johan-adriaans/SyringeHelper/stl-examples/BDUltraFine-U100-0-to-1.stl

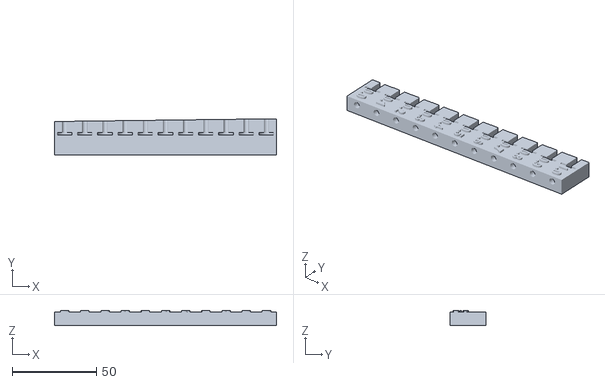
[picture p19: CAD file, 2025-03-12]
stl-examples/BDUltraFine-U100-0-to-1.stl
132.0 x 21.5 x 9.00
