johan-adriaans/SyringeHelper/stl-examples/BDUltraFine-U100-3-to-4.stl

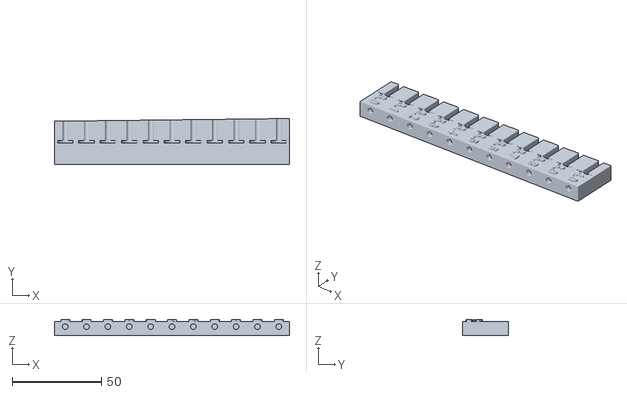
[picture p20: CAD file, 2025-03-12]
stl-examples/BDUltraFine-U100-3-to-4.stl
132.0 x 25.6 x 9.00
