johan-adriaans/SyringeHelper/stl-examples/SolVet-U40-1.6-to-2.5.stl

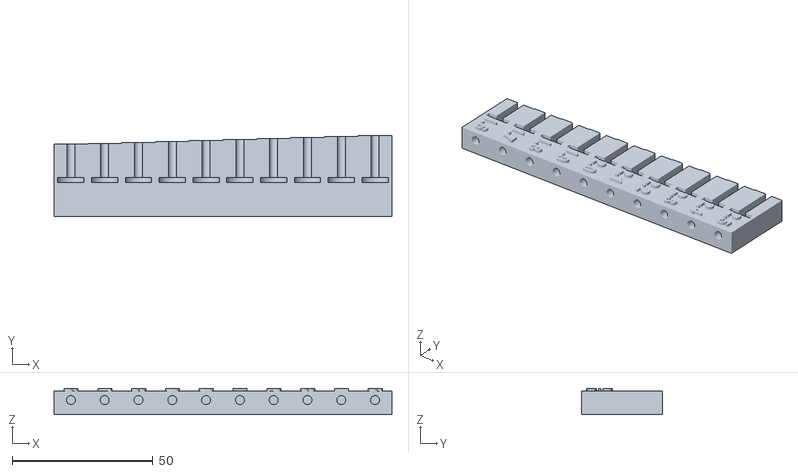
[picture p21: CAD file, 2024-09-01]
stl-examples/SolVet-U40-1.6-to-2.5.stl
120.0 x 28.8 x 9.40
