johan-adriaans/SyringeHelper/stl-examples/SolVet-U40-0.05-to-0.5.stl

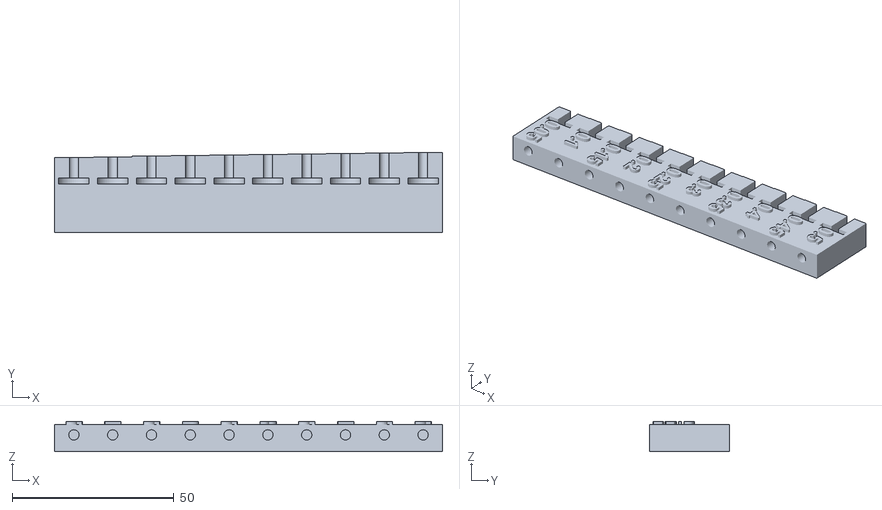
[picture p22: CAD file, 2024-09-01]
stl-examples/SolVet-U40-0.05-to-0.5.stl
120.0 x 24.9 x 9.40
