johan-adriaans/SyringeHelper/stl-examples/SolVet-U40-3.75-to-6.5.stl

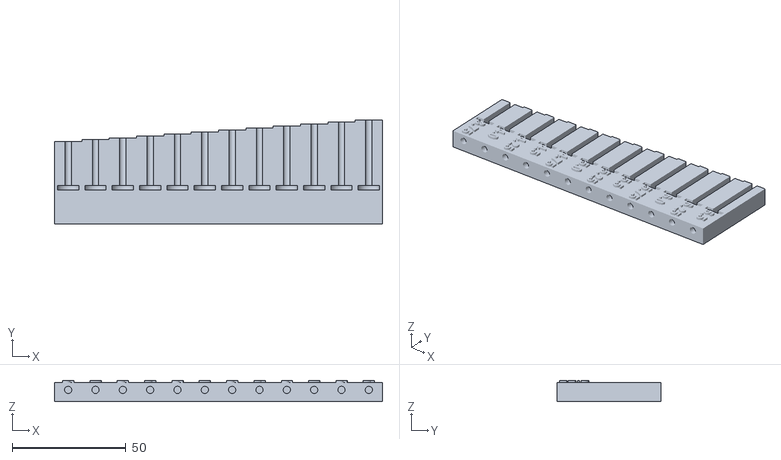
[picture p23: CAD file, 2024-09-01]
stl-examples/SolVet-U40-3.75-to-6.5.stl
144.0 x 45.6 x 9.40
