johan-adriaans/SyringeHelper/stl-examples/SolVet-U40-calibration.stl

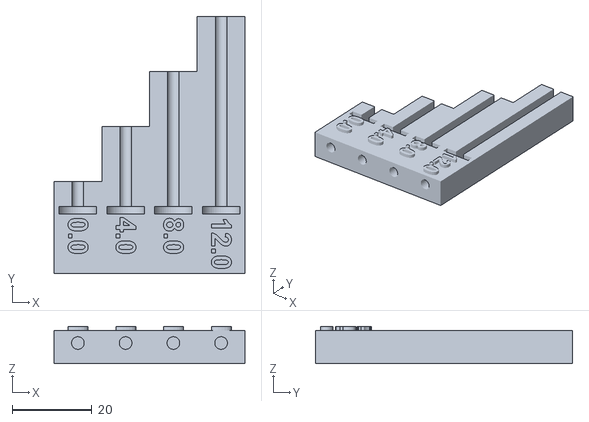
[picture p24: CAD file, 2024-09-01]
stl-examples/SolVet-U40-calibration.stl
48.0 x 64.6 x 9.40
