johan-adriaans/SyringeHelper/stl-examples/SolVet-U40-0.75-to-3.5.stl

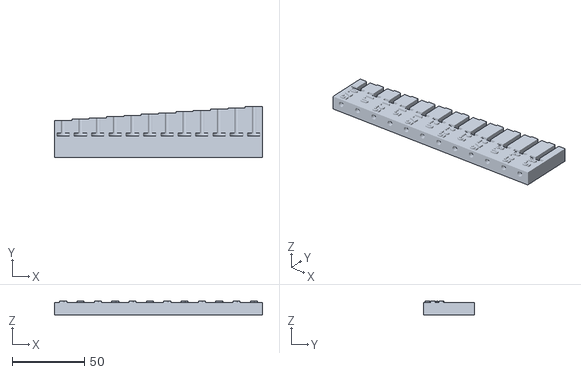
[picture p25: CAD file, 2024-09-01]
stl-examples/SolVet-U40-0.75-to-3.5.stl
144.0 x 35.2 x 9.40
