johan-adriaans/SyringeHelper/stl-examples/SolVet-U100-1-to-3.5.stl

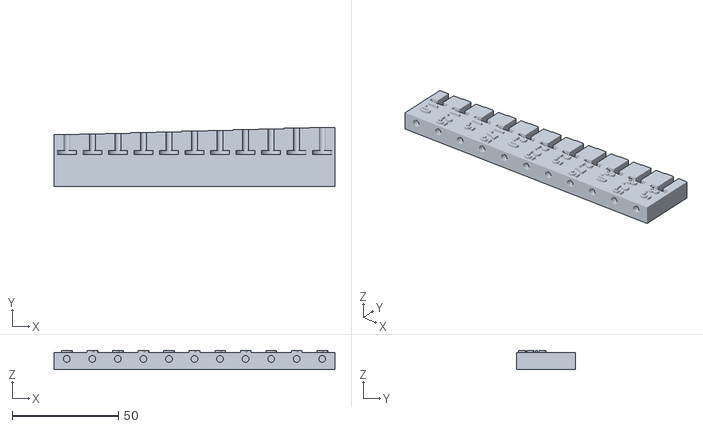
[picture p26: CAD file, 2024-05-23]
stl-examples/SolVet-U100-1-to-3.5.stl
132.0 x 27.9 x 9.00
