johan-adriaans/SyringeHelper/stl-examples/SolVet-U100-3.75-to-6.stl

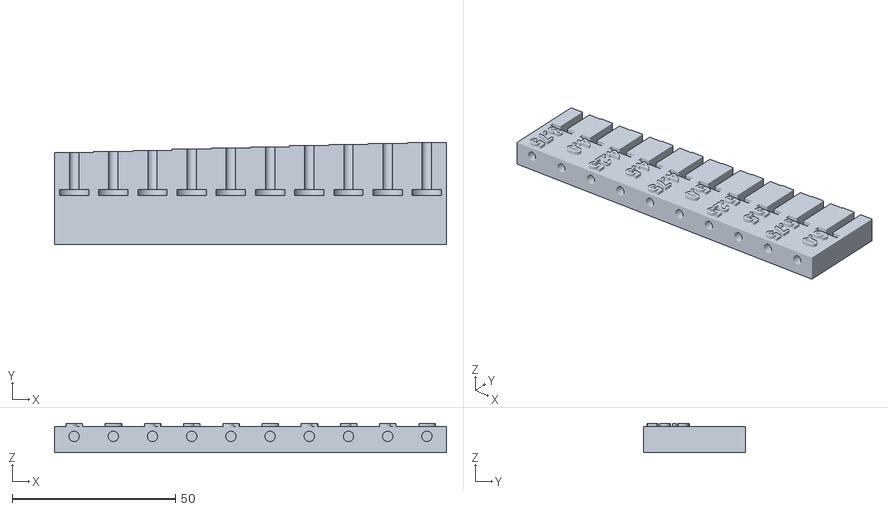
[picture p27: CAD file, 2024-05-23]
stl-examples/SolVet-U100-3.75-to-6.stl
120.0 x 31.3 x 9.00
