johan-adriaans/SyringeHelper/stl-examples/SolVet-U100-6-to-7.stl

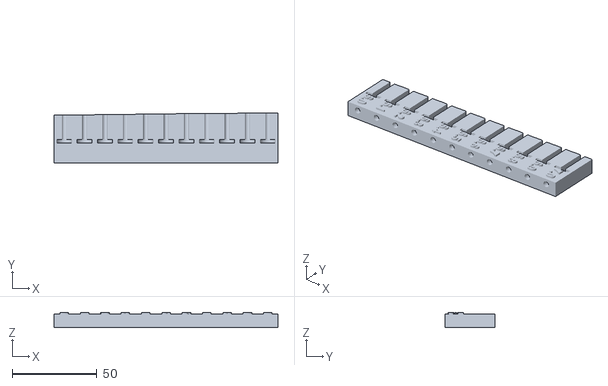
[picture p28: CAD file, 2024-05-23]
stl-examples/SolVet-U100-6-to-7.stl
132.0 x 29.7 x 9.00
