johan-adriaans/SyringeHelper/stl-examples/SolVet-U100-4-to-5.stl

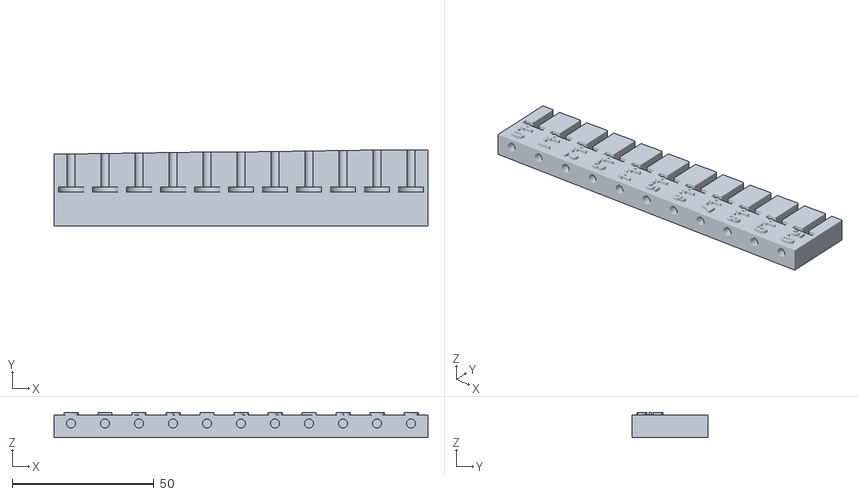
[picture p29: CAD file, 2024-05-23]
stl-examples/SolVet-U100-4-to-5.stl
132.0 x 26.9 x 9.00
