johan-adriaans/SyringeHelper/stl-examples/SolVet-U100-7-to-8.stl

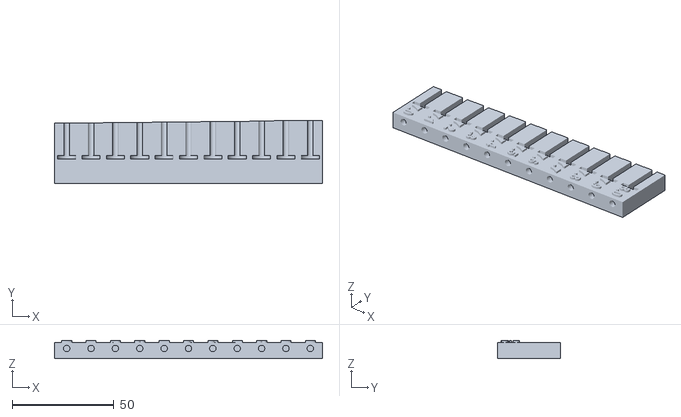
[picture p30: CAD file, 2024-05-23]
stl-examples/SolVet-U100-7-to-8.stl
132.0 x 31.1 x 9.00
