johan-adriaans/SyringeHelper/stl-examples/SolVet-U100-8-to-9.stl

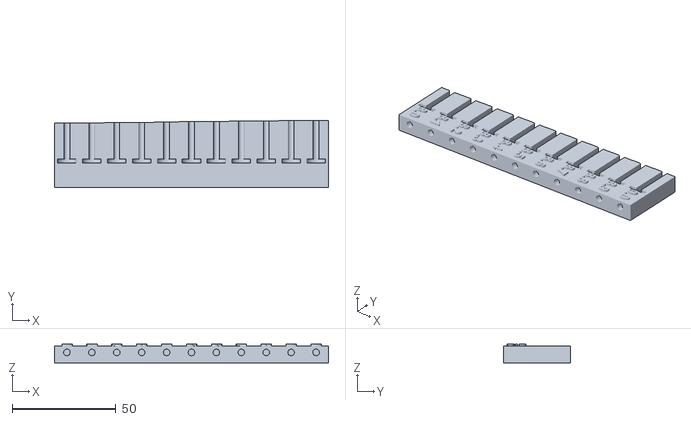
[picture p31: CAD file, 2024-05-23]
stl-examples/SolVet-U100-8-to-9.stl
132.0 x 32.5 x 9.00
