johan-adriaans/SyringeHelper/stl-examples/SolVet-U100-calibration.stl

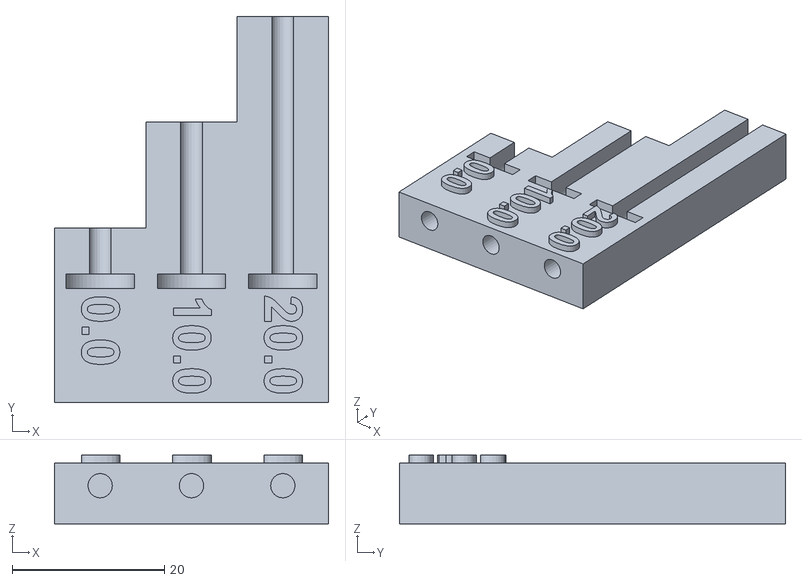
[picture p32: CAD file, 2024-05-23]
stl-examples/SolVet-U100-calibration.stl
36.0 x 50.8 x 9.00
