johan-adriaans/SyringeHelper/stl-examples/BDMicroFine-U100-4-to-5.stl

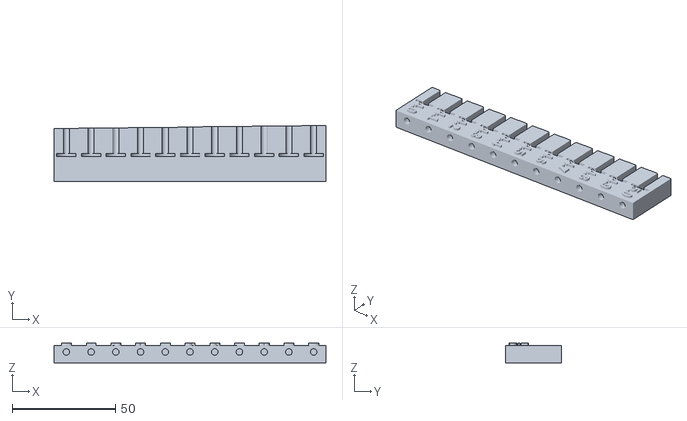
[picture p33: CAD file, 2023-01-15]
stl-examples/BDMicroFine-U100-4-to-5.stl
132.0 x 27.1 x 9.50
