johan-adriaans/SyringeHelper/stl-examples/BDMicroFine-U100-7-to-8.stl

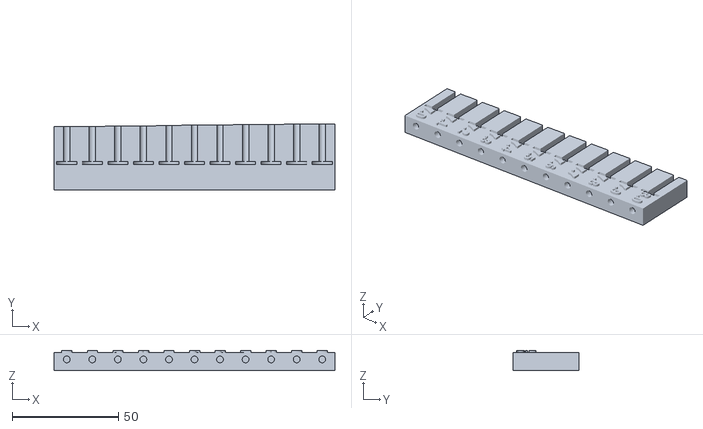
[picture p34: CAD file, 2023-01-15]
stl-examples/BDMicroFine-U100-7-to-8.stl
132.0 x 31.2 x 9.50
