johan-adriaans/SyringeHelper/stl-examples/BDMicroFine-U40-6-to-7.stl

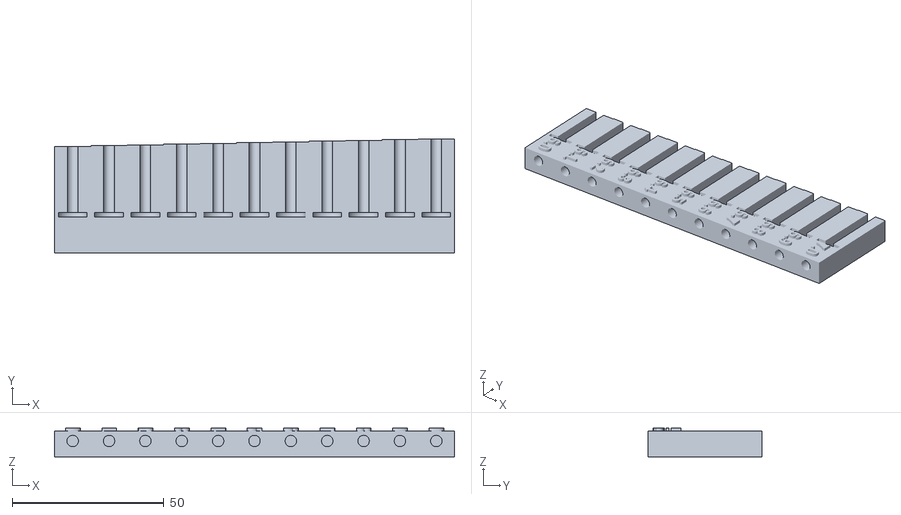
[picture p35: CAD file, 2023-01-15]
stl-examples/BDMicroFine-U40-6-to-7.stl
132.0 x 37.8 x 9.50
