johan-adriaans/SyringeHelper/stl-examples/BDMicroFine-U100-1-to-2.stl

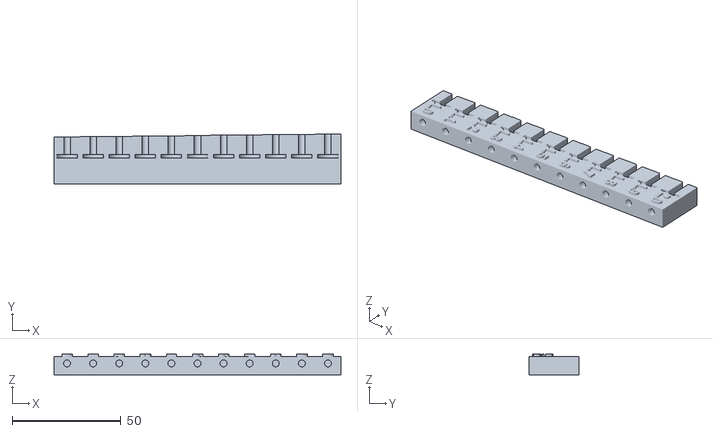
[picture p36: CAD file, 2023-01-15]
stl-examples/BDMicroFine-U100-1-to-2.stl
132.0 x 23.0 x 9.50
