johan-adriaans/SyringeHelper/stl-examples/BDMicroFine-U40-3-to-4.stl

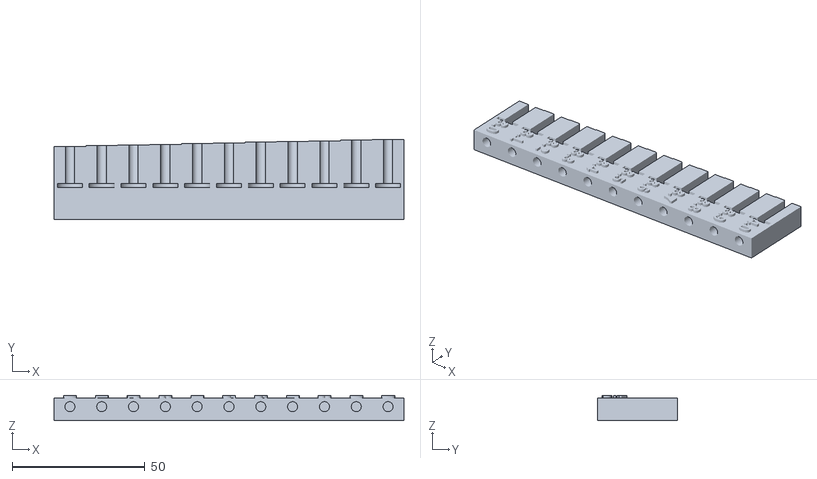
[picture p37: CAD file, 2023-01-15]
stl-examples/BDMicroFine-U40-3-to-4.stl
132.0 x 30.1 x 9.50
