johan-adriaans/SyringeHelper/stl-examples/BDMicroFine-U40-1-to-2.stl

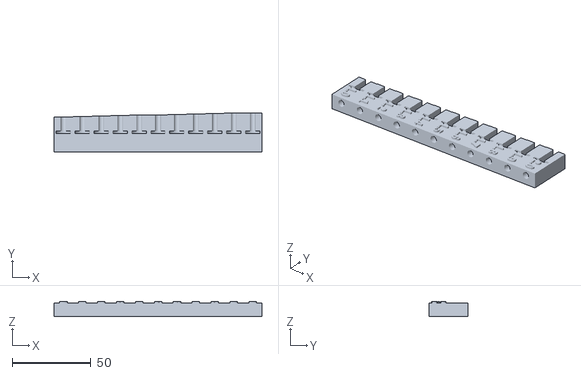
[picture p38: CAD file, 2023-01-15]
stl-examples/BDMicroFine-U40-1-to-2.stl
132.0 x 25.0 x 9.50
