johan-adriaans/SyringeHelper/stl-examples/BDMicroFine-U40-calibration.stl

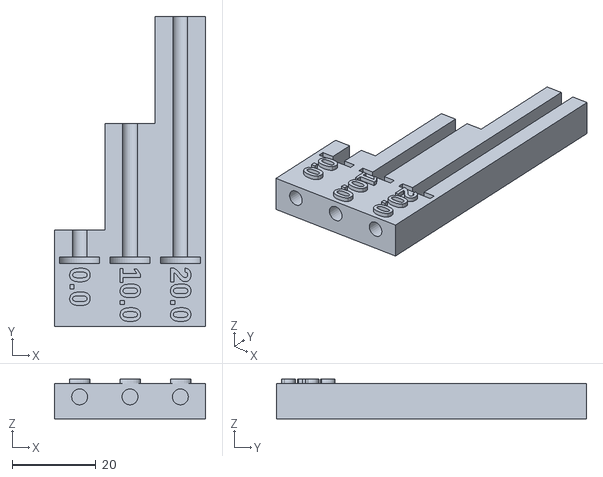
[picture p39: CAD file, 2023-01-15]
stl-examples/BDMicroFine-U40-calibration.stl
36.0 x 73.8 x 9.50
