johan-adriaans/SyringeHelper/stl-examples/BDMicroFine-U40-0-to-1.stl

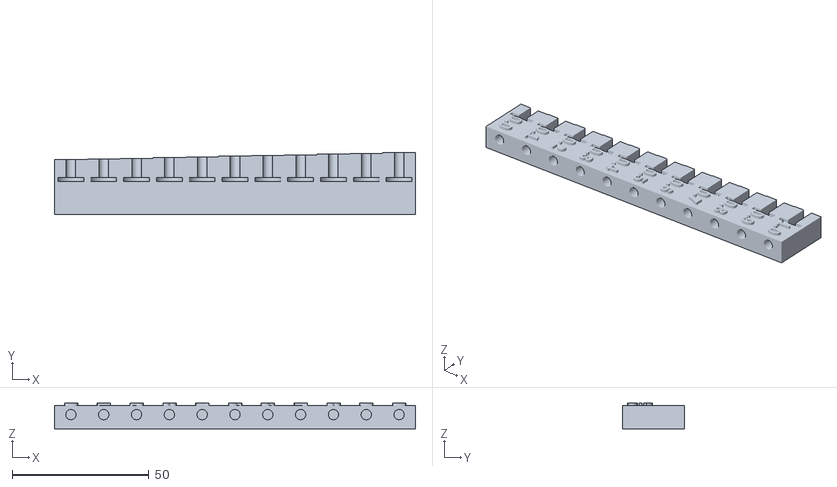
[picture p40: CAD file, 2023-01-15]
stl-examples/BDMicroFine-U40-0-to-1.stl
132.0 x 22.5 x 9.50
