johan-adriaans/SyringeHelper/stl-examples/BDMicroFine-U100-0-to-1.stl

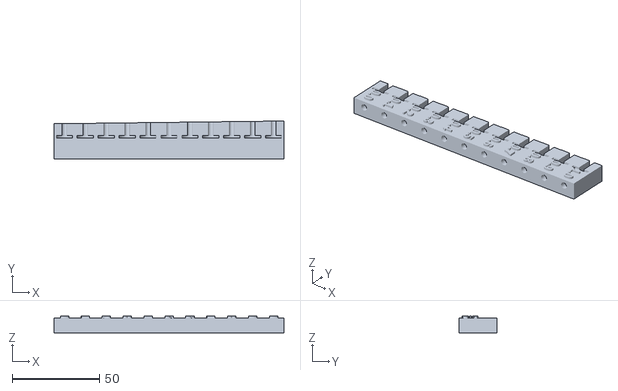
[picture p41: CAD file, 2023-01-15]
stl-examples/BDMicroFine-U100-0-to-1.stl
132.0 x 21.6 x 9.50
