johan-adriaans/SyringeHelper/stl-examples/BDMicroFine-U100-calibration.stl

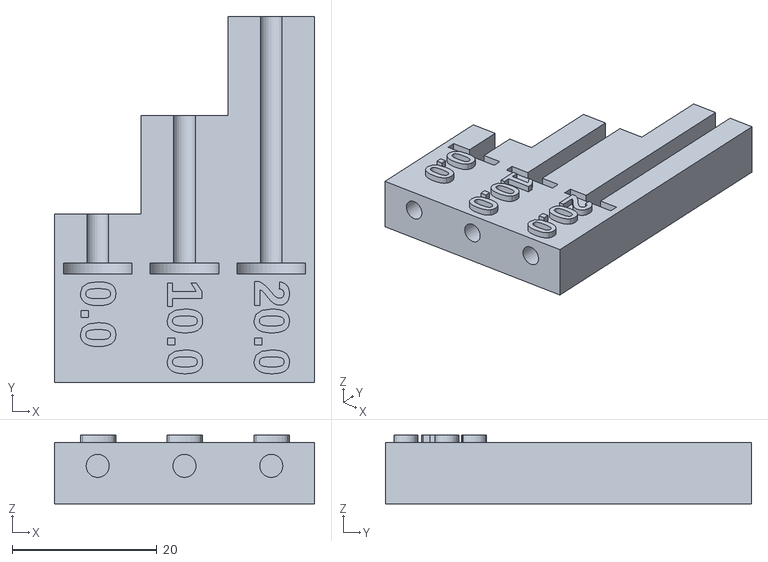
[picture p42: CAD file, 2023-01-15]
stl-examples/BDMicroFine-U100-calibration.stl
36.0 x 50.6 x 9.50
