johan-adriaans/SyringeHelper/stl-examples/BDMicroFine-U40-5-to-6.stl

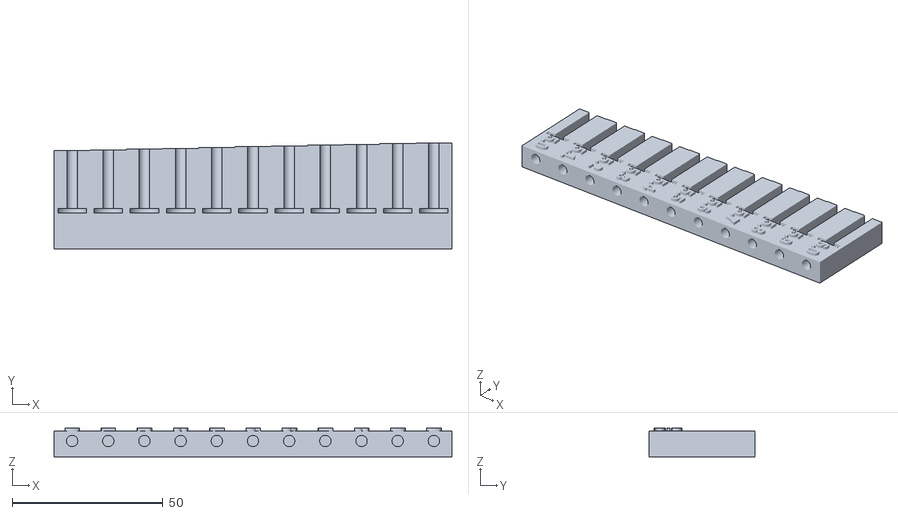
[picture p43: CAD file, 2023-01-15]
stl-examples/BDMicroFine-U40-5-to-6.stl
132.0 x 35.2 x 9.50
