johan-adriaans/SyringeHelper/stl-examples/BDMicroFine-U100-8-to-9.stl

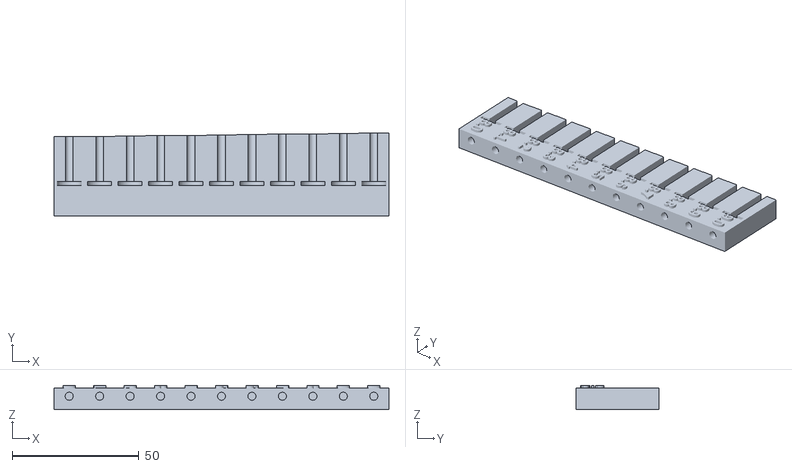
[picture p44: CAD file, 2023-01-15]
stl-examples/BDMicroFine-U100-8-to-9.stl
132.0 x 32.6 x 9.50
