johan-adriaans/SyringeHelper/stl-examples/BDMicroFine-U100-3-to-4.stl

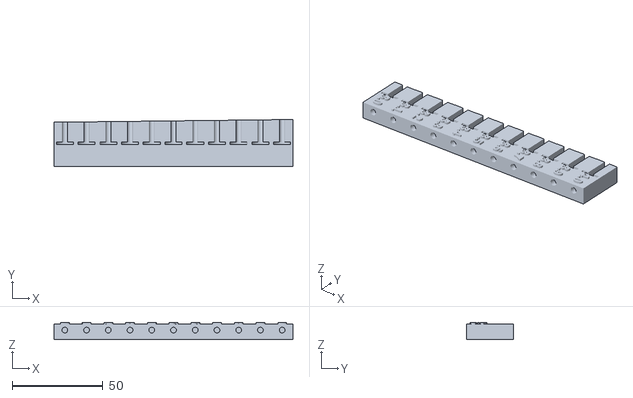
[picture p45: CAD file, 2023-01-15]
stl-examples/BDMicroFine-U100-3-to-4.stl
132.0 x 25.7 x 9.50
