johan-adriaans/SyringeHelper/stl-examples/BDMicroFine-U100-5-to-6.stl

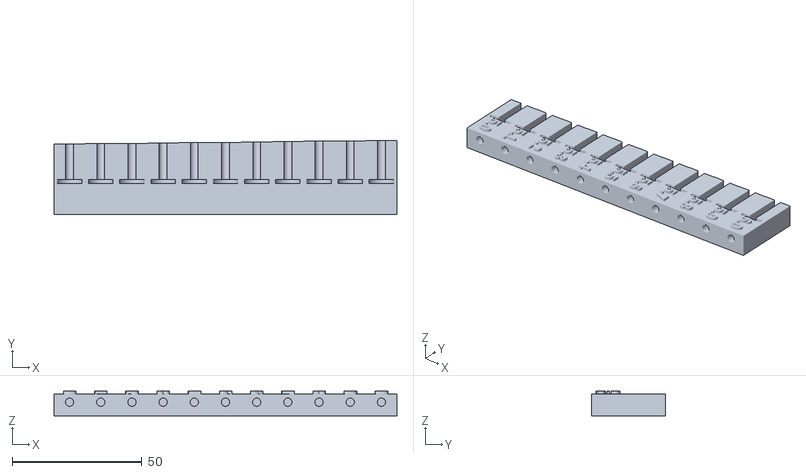
[picture p46: CAD file, 2023-01-15]
stl-examples/BDMicroFine-U100-5-to-6.stl
132.0 x 28.5 x 9.50
