johan-adriaans/SyringeHelper/stl-examples/BDMicroFine-U40-8-to-9.stl

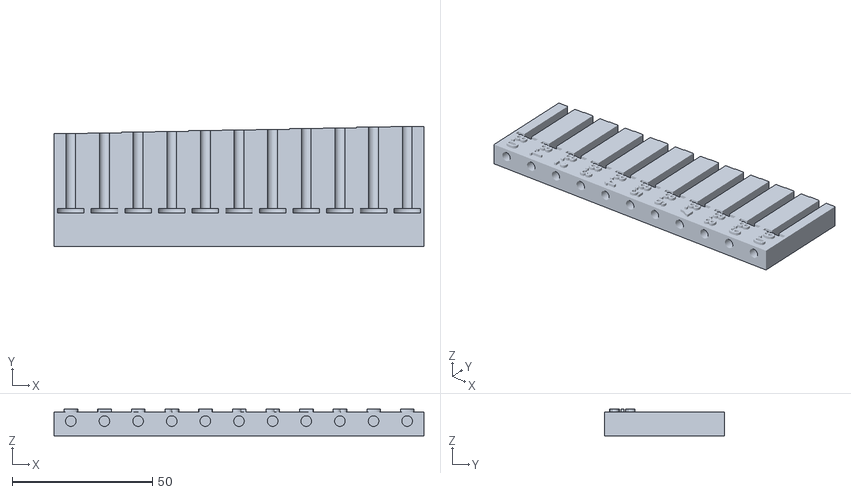
[picture p47: CAD file, 2023-01-15]
stl-examples/BDMicroFine-U40-8-to-9.stl
132.0 x 42.9 x 9.50
