johan-adriaans/SyringeHelper/stl-examples/BDMicroFine-U100-2-to-3.stl

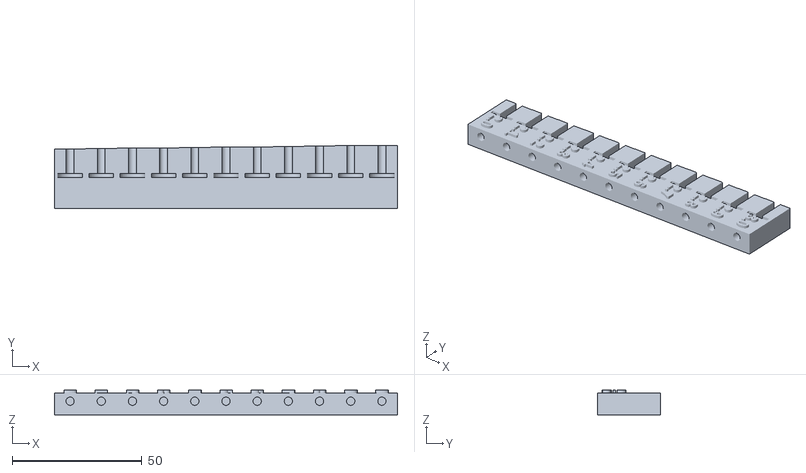
[picture p48: CAD file, 2023-01-15]
stl-examples/BDMicroFine-U100-2-to-3.stl
132.0 x 24.4 x 9.50
