johan-adriaans/SyringeHelper/stl-examples/BDMicroFine-U40-7-to-8.stl

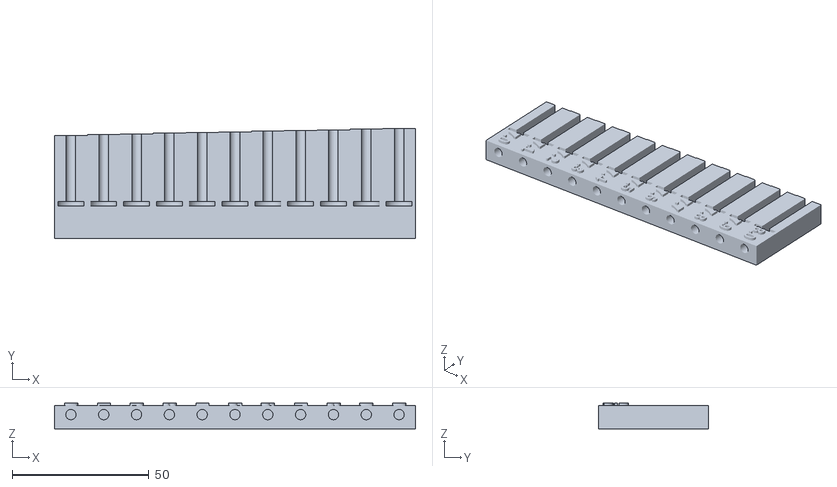
[picture p49: CAD file, 2023-01-15]
stl-examples/BDMicroFine-U40-7-to-8.stl
132.0 x 40.3 x 9.50
