johan-adriaans/SyringeHelper/stl-examples/BDMicroFine-U40-2-to-3.stl

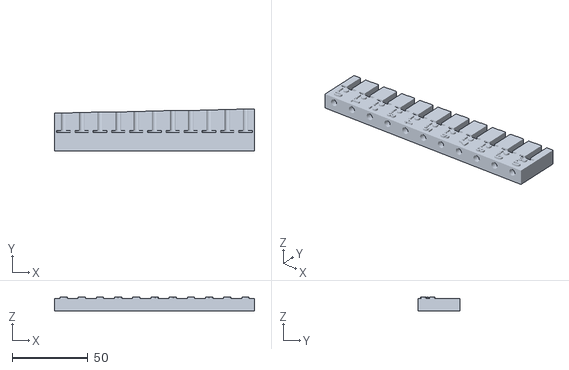
[picture p50: CAD file, 2023-01-15]
stl-examples/BDMicroFine-U40-2-to-3.stl
132.0 x 27.6 x 9.50
